m24842/OpenForge/cad/side_separating.SLDPRT

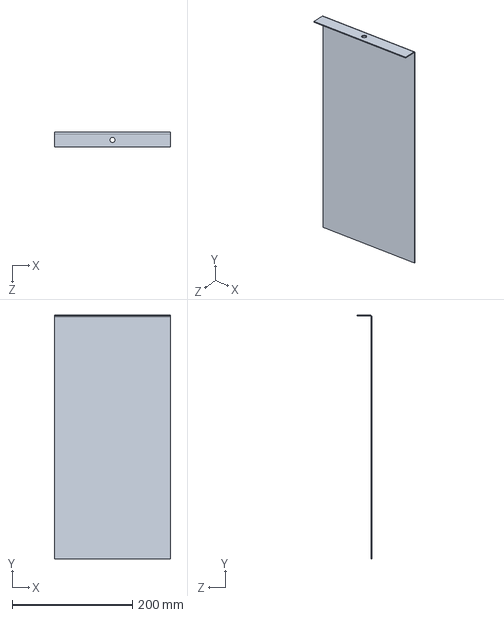
[picture p22: CAD file, 2026-04-27]
cad/side_separating.SLDPRT
193.7 x 406.4 x 25.4 mm
