m24842/OpenForge/cad/Turn Knob.SLDPRT

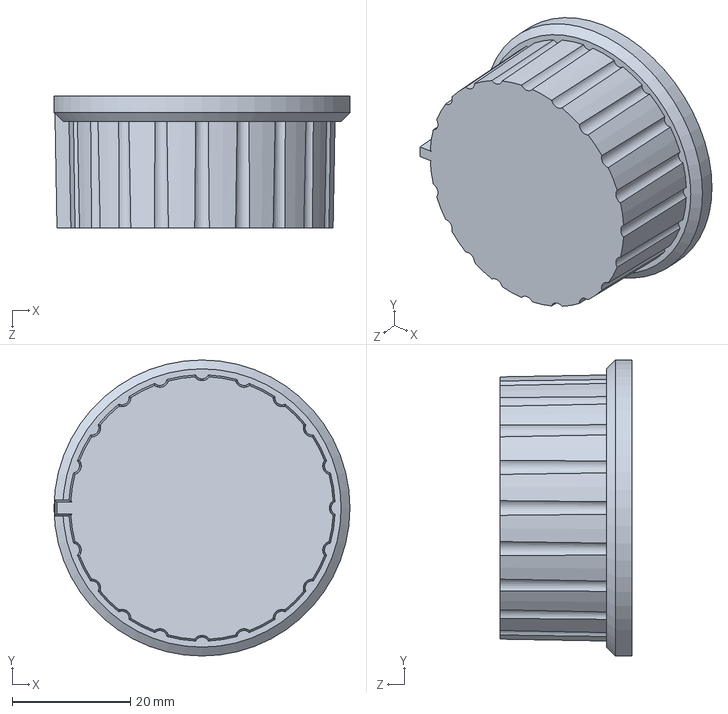
[picture p23: CAD file, 2026-04-27]
cad/Turn Knob.SLDPRT
50.0 x 50.0 x 22.3 mm
