m24842/OpenForge/cad/PYM_303012_pin.SLDPRT

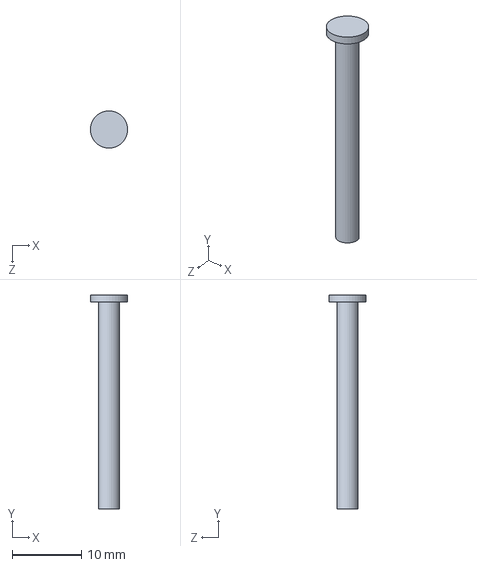
[picture p24: CAD file, 2026-04-27]
cad/PYM_303012_pin.SLDPRT
5.38 x 31.0 x 5.40 mm
