m24842/OpenForge/cad/Top_bottom_elec.SLDPRT

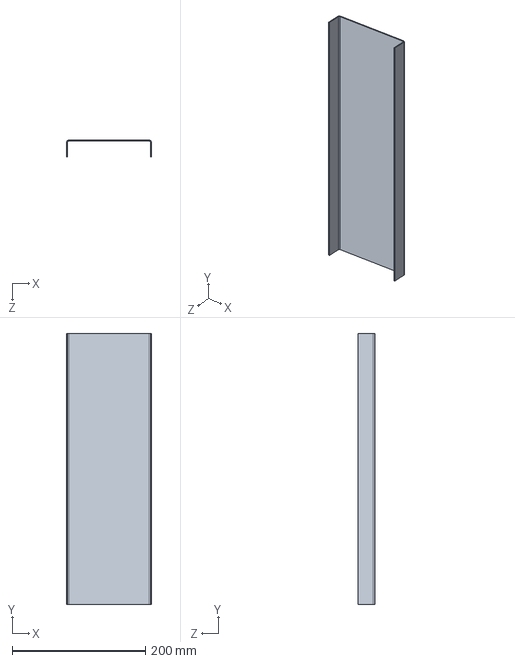
[picture p25: CAD file, 2026-04-27]
cad/Top_bottom_elec.SLDPRT
127.0 x 406.4 x 25.4 mm
