m24842/OpenForge/cad/12V Diaphragm Pump RS-385 - WITH BRACKETS.SLDASM

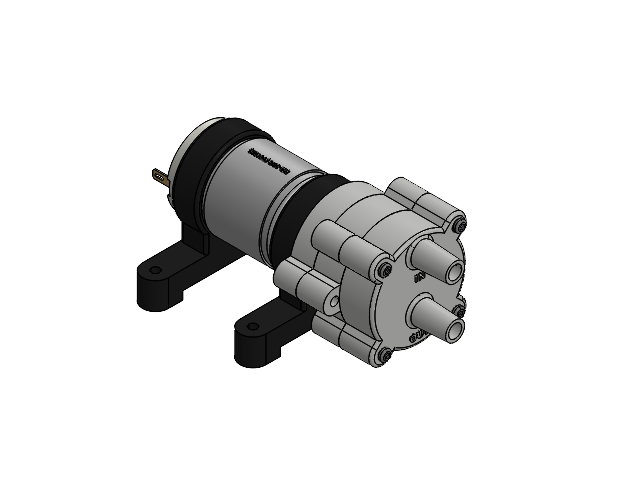
[picture p26: CAD file, 2026-04-27]
cad/12V Diaphragm Pump RS-385 - WITH BRACKETS.SLDASM
Motor_Main.iges
Pump_Main.iges
99397A195.iges x 6
Rubber_Bracket.iges x 2
