m24842/OpenForge/pcb/ZVS_circuit_kit.asc

C1: cap; 0.33µ
C2: cap; 0.33µ
C3: cap; 0.33µ
C4: cap; 0.33µ
C5: cap; 0.33µ
C6: cap; 0.33µ
C7: cap; 0.33µ
C8: cap; 0.33µ
C9: cap; 0.33µ
C10: cap; 0.33µ
C11: cap; 0.33µ
C12: cap; 0.33µ
D1: zener; BZX84C12L
D2: zener; BZX84C12L
D3: zener; BZX84C12L
D4: zener; BZX84C12L
D5: zener; BZX84C12L
D6: zener; BZX84C12L
D7: schottky; 1N5817
D8: schottky; 1N5817
D9: schottky; 1N5817
D10: schottky; 1N5817
D11: schottky; 1N5817
D12: schottky; 1N5817
L1: ind; 100µ
L2: ind; 100µ
L3: ind; 76.7µ
M1: nmos; IRFP240
M2: nmos; IRFP240
M3: nmos; IRFP240
M4: nmos; IRFP240
M5: nmos; IRFP240
M6: nmos; IRFP240
R1: res; 10k
R2: res; 10k
R3: res; 10k
R4: res; 10k
R5: res; 10k
R6: res; 10k
R7: res; 470
R8: res; 470
R9: res; 470
R10: res; 470
R11: res; 470
R12: res; 470
V1: voltage; 48; Rser=0.05
Named nets: VDD, 0
.tran 0.05 startup
